tomaskovacik/vag_door_indicator/20200819_131400.jpg

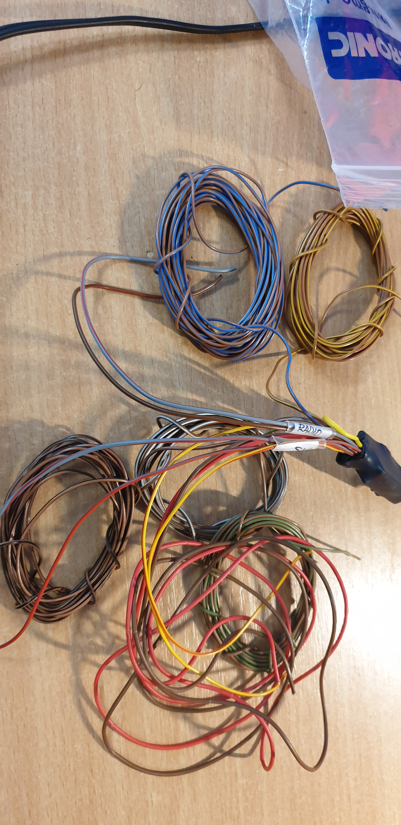
20200819_131400.jpg
