tomaskovacik/vag_door_indicator/HW/audi_a4 door_indicator.kicad_sch

## KiCad design HW/audi_a4 door_indicator.kicad_sch (2023-05-16, an earlier design)

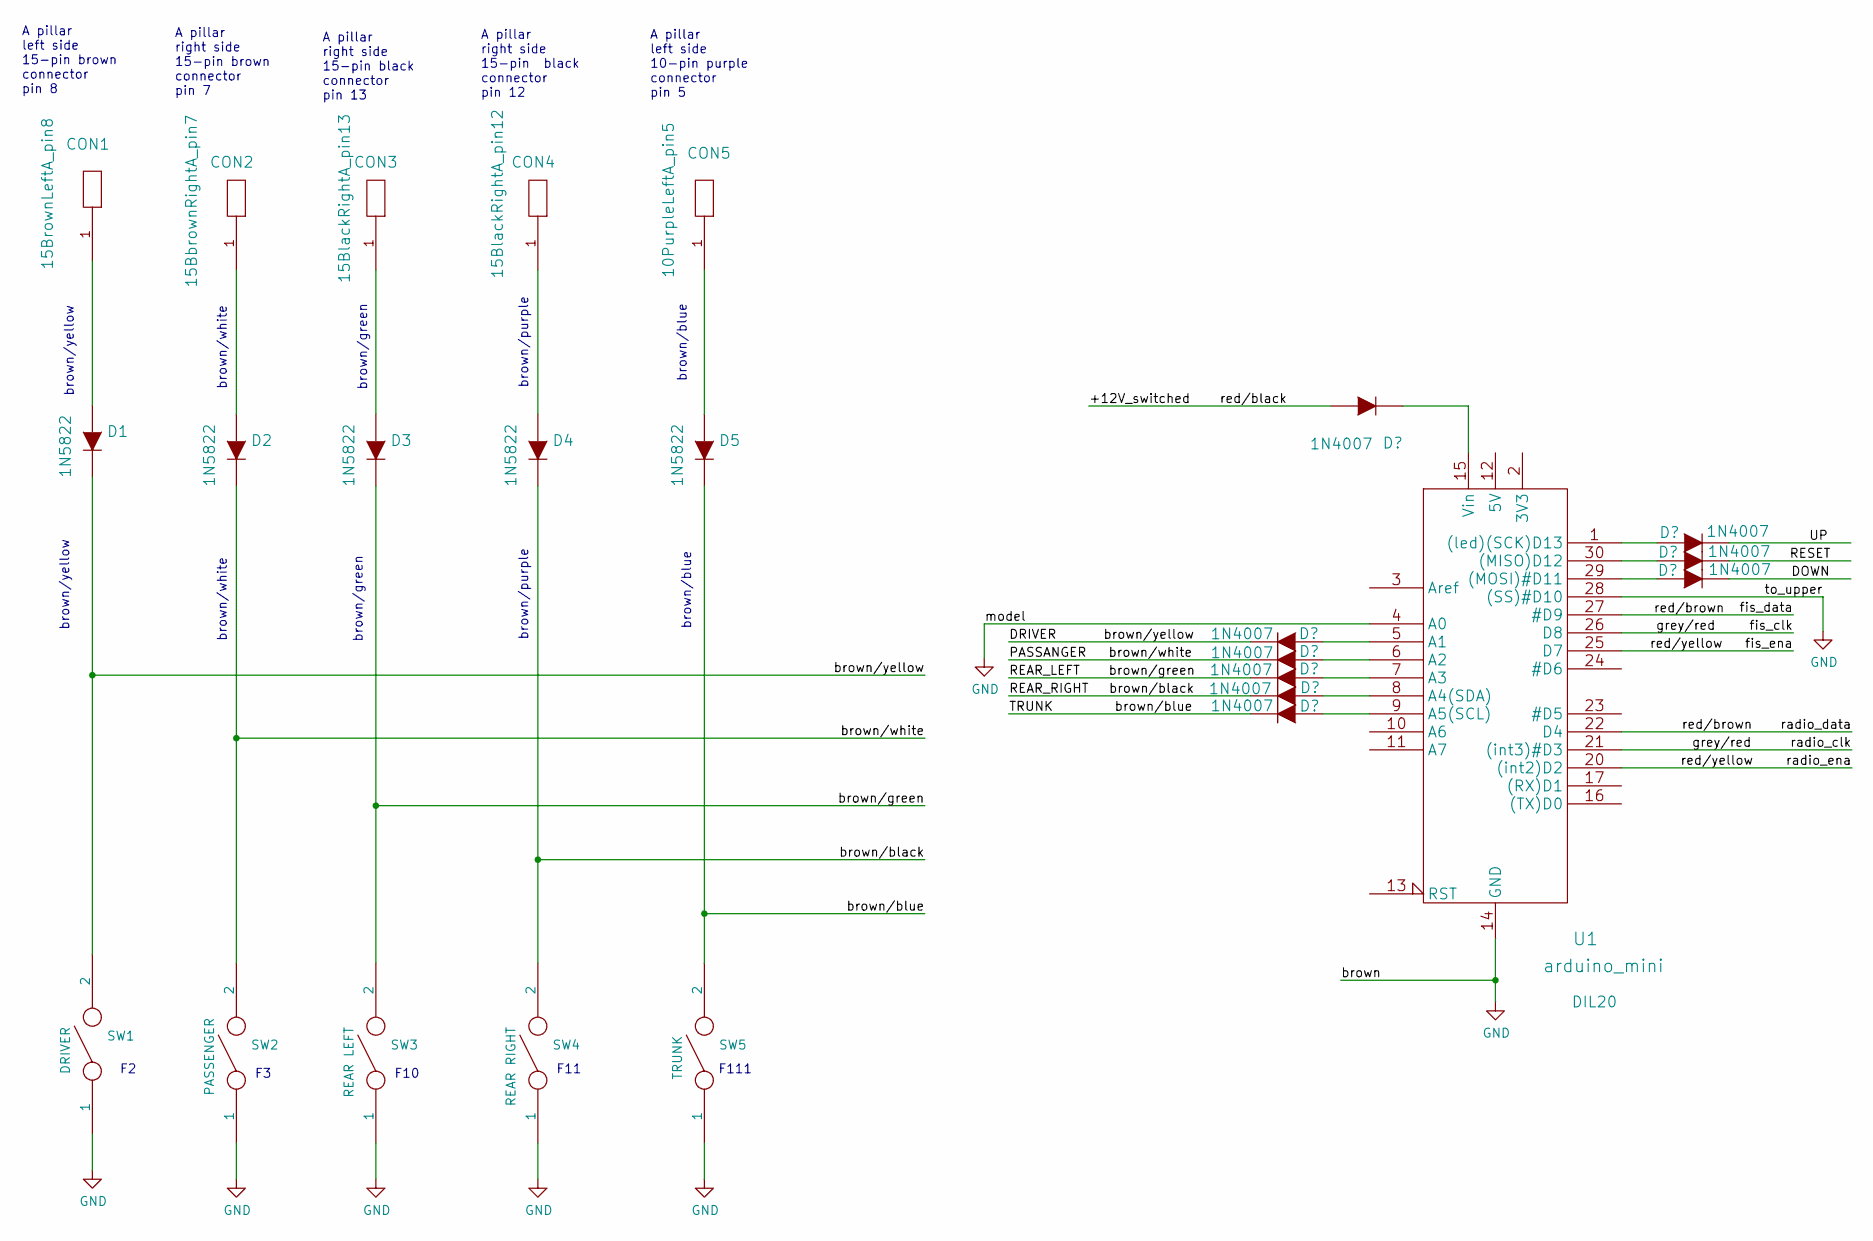
[picture p5: schematic audi_a4 door_indicator.kicad_sch]

Parts:
CON1: 15BrownLeftA_pin8
CON2: 15BbrownRightA_pin7
CON3: 15BlackRightA_pin13
CON4: 15BlackRightA_pin12
CON5: 10PurpleLeftA_pin5
D1, D2, D3, D4, D5: 1N5822
SW1: DRIVER
SW2: PASSENGER
SW3: REAR LEFT
SW4: REAR RIGHT
SW5: TRUNK
U1: arduino_mini; DIL20

Connections:
GND: SW1.1, SW2.1, SW3.1, SW4.1, SW5.1, U1.14 (GND)
unnamed: CON1.1, D1.1 (A)
unnamed: CON2.1, D2.1 (A)
unnamed: CON3.1, D3.1 (A)
unnamed: CON4.1, D4.1 (A)
unnamed: CON5.1, D5.1 (A)
brown/black: D4.2 (K), SW4.2
brown/blue: D5.2 (K), SW5.2
brown/green: D3.2 (K), SW3.2
brown/white: D2.2 (K), SW2.2
brown/yellow: D1.2 (K), SW1.2
fis_clk: U1.21 ((int3)#D3), U1.26 (D8)
fis_data: U1.27 (#D9)
fis_ena: U1.20 ((int2)D2), U1.25 (D7)
model: U1.4 (A0)
radio_data: U1.22 (D4)
to_upper: U1.28 ((SS)#D10)

Notes on the sheet:
brown/yellow
A pillar right side 15-pin black connector pin 12
F10
A pillar right side 15-pin black connector pin 13
F11
A pillar right side 15-pin brown connector pin 7
F111
brown/blue
brown/white
A pillar left side 15-pin brown connector pin 8
brown/green
brown/purple
A pillar left side 10-pin purple connector pin 5
