tomaskovacik/vag_door_indicator/SW/2.0sw/var_door_indicator/bitmaps.h

const uint8_t PROGMEM b5f_orezana2[528] = {
0x00,0x00,0x00,0x00,0x00,0x00
,0x00,0x00,0x00,0x00,0x00,0x00
,0x00,0x03,0xff,0xe0,0x01,0xc0
,0x00,0x07,0xff,0xf0,0x0f,0xc0
,0x00,0x0f,0xff,0xf8,0x7f,0xc0
,0x3e,0x1f,0xff,0xfc,0x7f,0xc0
,0x3e,0x1f,0xff,0xfc,0x7f,0xc0
,0x3e,0x1f,0xff,0xfc,0x7f,0xc0
,0x3e,0x3f,0xff,0xfe,0x79,0x80
,0x3e,0x3f,0xff,0xfe,0x7f,0xc0
,0x3e,0x3f,0xff,0xfe,0x7f,0xc0
,0x3e,0x3f,0xff,0xfe,0x7f,0xc0
,0x3e,0x3f,0xff,0xfe,0x7f,0xc0
,0x3e,0x3f,0xff,0xff,0x0f,0xc0
,0x3e,0x3f,0xff,0xff,0x01,0xc0
,0x3e,0x3f,0xff,0xff,0x00,0x00
,0x3e,0x3f,0xff,0xff,0x7f,0xc0
,0x3e,0x3f,0xff,0xff,0x7f,0xc0
,0x3e,0x3e,0x00,0x1f,0x7f,0xc0
,0x3e,0x3e,0x00,0x1f,0x7f,0xc0
,0x3e,0x3e,0x00,0x1f,0x7f,0xc0
,0x3e,0x3e,0x00,0x1f,0x7f,0xc0
,0x3e,0x1e,0x00,0x1f,0x00,0x40
,0x3e,0x1e,0x00,0x7f,0x00,0xc0
,0x3f,0xfb,0x8f,0xff,0x00,0xc0
,0x0f,0xfa,0x8f,0xff,0x00,0xc0
,0x00,0xec,0x8f,0xff,0x7f,0xc0
,0x00,0x79,0x8f,0xff,0x7f,0xc0
,0x00,0x20,0x8f,0xfe,0x7f,0xc0
,0x00,0x3a,0x0f,0xfe,0x7f,0xc0
,0x20,0x1b,0x0f,0xfe,0x7f,0xc0
,0x30,0x1e,0x0f,0xfe,0x00,0x00
,0x38,0x00,0x8f,0xfe,0x00,0x00
,0x3c,0x00,0x0f,0xfc,0x7f,0xc0
,0x3f,0xc0,0x0f,0xfc,0x7f,0xc0
,0x3f,0xe0,0x0f,0xfc,0x7f,0xc0
,0x3f,0xe0,0x0f,0xf8,0x7f,0xc0
,0x3f,0xe0,0x07,0xf0,0x7f,0xc0
,0x3f,0xe0,0x03,0xe0,0x7f,0xc0
,0x00,0xe2,0x01,0xc0,0x00,0x00
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
};

const uint8_t PROGMEM b5f_orezana[64*88] = {
0xff,0xff,0xff,0xff,0xff,0xff,0xff,0xff
,0xff,0xff,0xff,0xff,0xff,0xff,0xff,0xff
,0xff,0xff,0xf0,0x00,0x01,0xff,0xff,0xc3
,0xff,0xff,0xc0,0x00,0x00,0x7f,0xf8,0x03
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
,0x3f,0xff,0xff,0xf1,0x00,0x44,0x01,0x00
,0x3f,0xff,0xff,0xf1,0x00,0x44,0x01,0x00
,0x3f,0xff,0xff,0xe2,0x00,0x88,0x01,0x00
,0x7f,0xff,0xff,0xe2,0x00,0x88,0x02,0x00
,0x7f,0xff,0xff,0xe2,0x00,0x88,0x02,0x00
,0xff,0xff,0xff,0xc4,0x01,0x10,0x04,0x00
,0xff,0xff,0xff,0xc7,0xff,0x1f,0xfc,0x00
};*/
